ijnekenamay/M8HeadlessStaging/image3.jpg

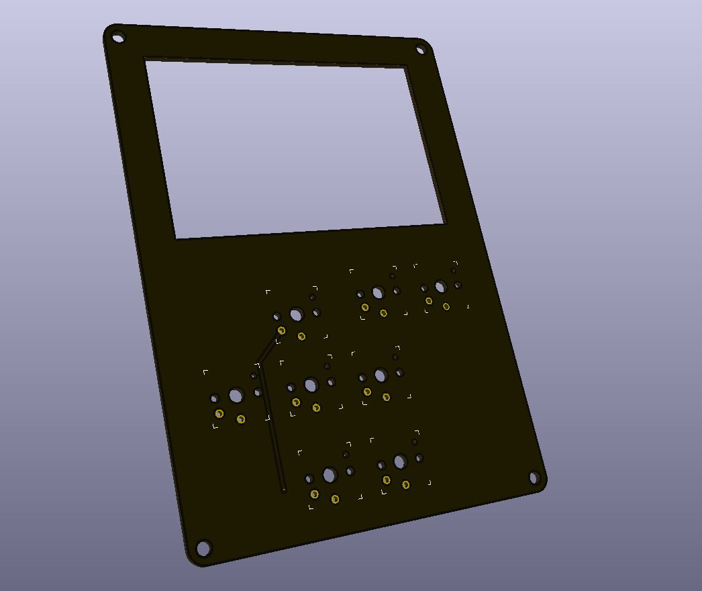
image3.jpg
