ijnekenamay/M8HeadlessStaging/image4.jpg

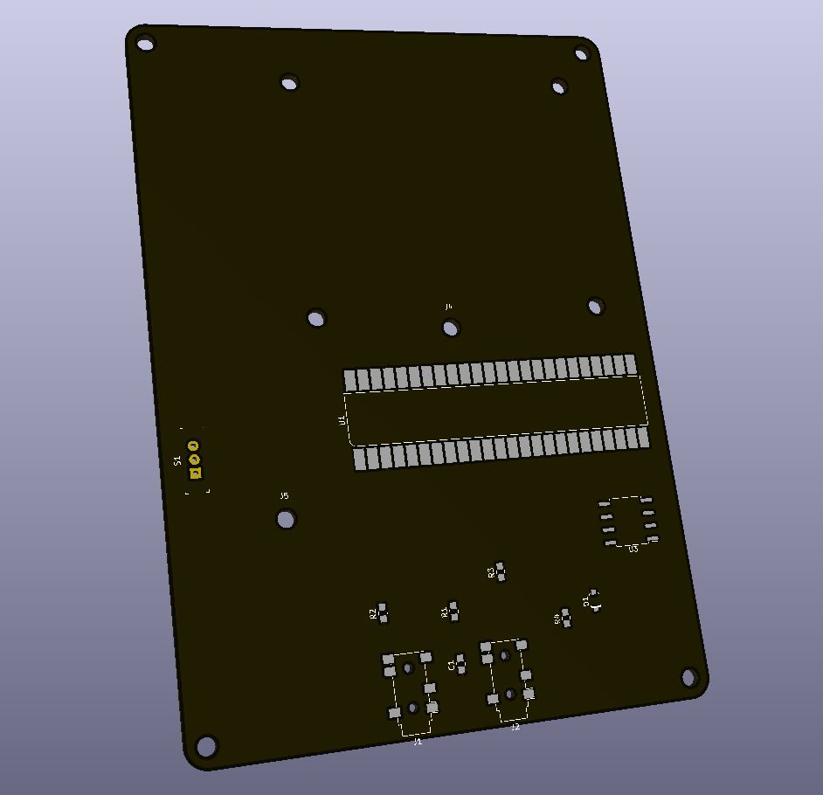
image4.jpg
